rhaamo/ARP-2600/schematics/4022 Noise.pdf

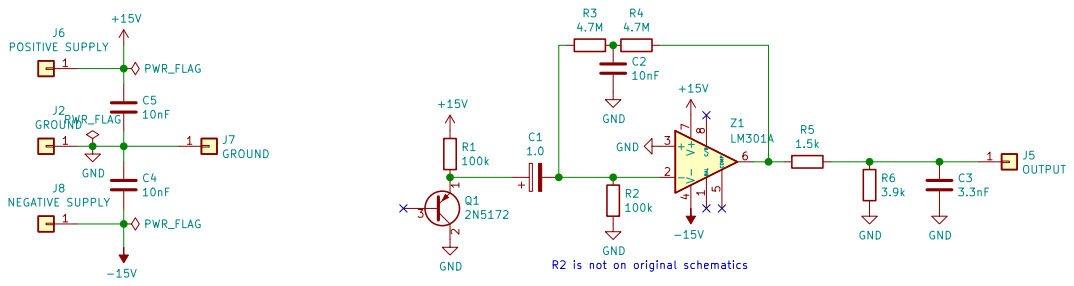
[picture p10: page 1]

R2 is not on original schematics

Id: 1/1 Title: File: 4022 Noise.sch Sheet: /
