rhaamo/ARP-2600/schematics/Board 1.pdf

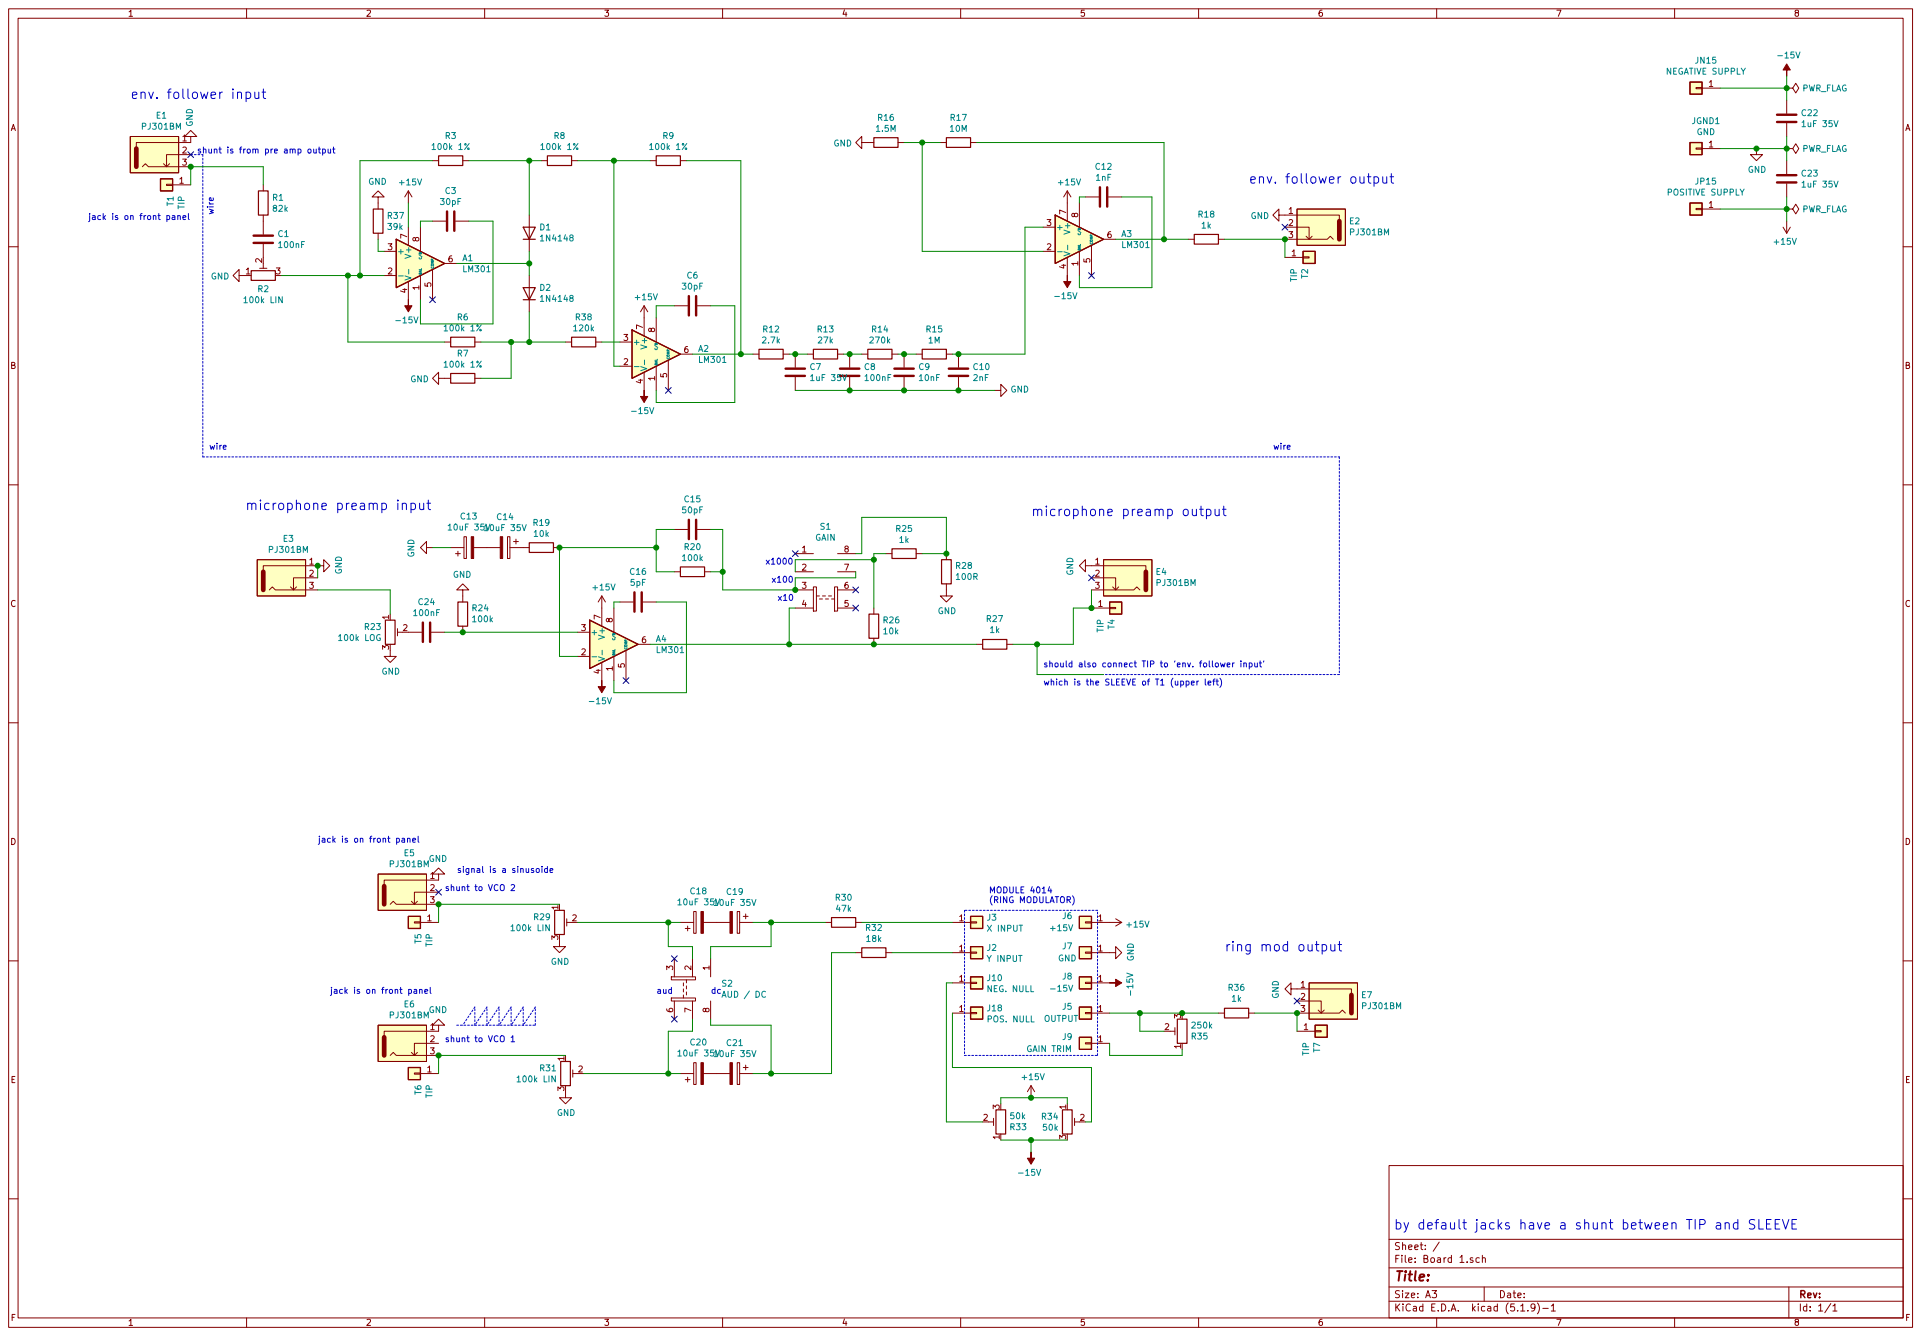
[picture p16: page 1]

shunt is from pre amp output

jack is on front panel

should also connect TIP to 'env. follower input' MODULE 4014

which is the SLEEVE of T1 (upper left) dc

by default jacks have a shunt between TIP and SLEEVE
