rhaamo/ARP-2600/schematics/4020 ADSR.pdf

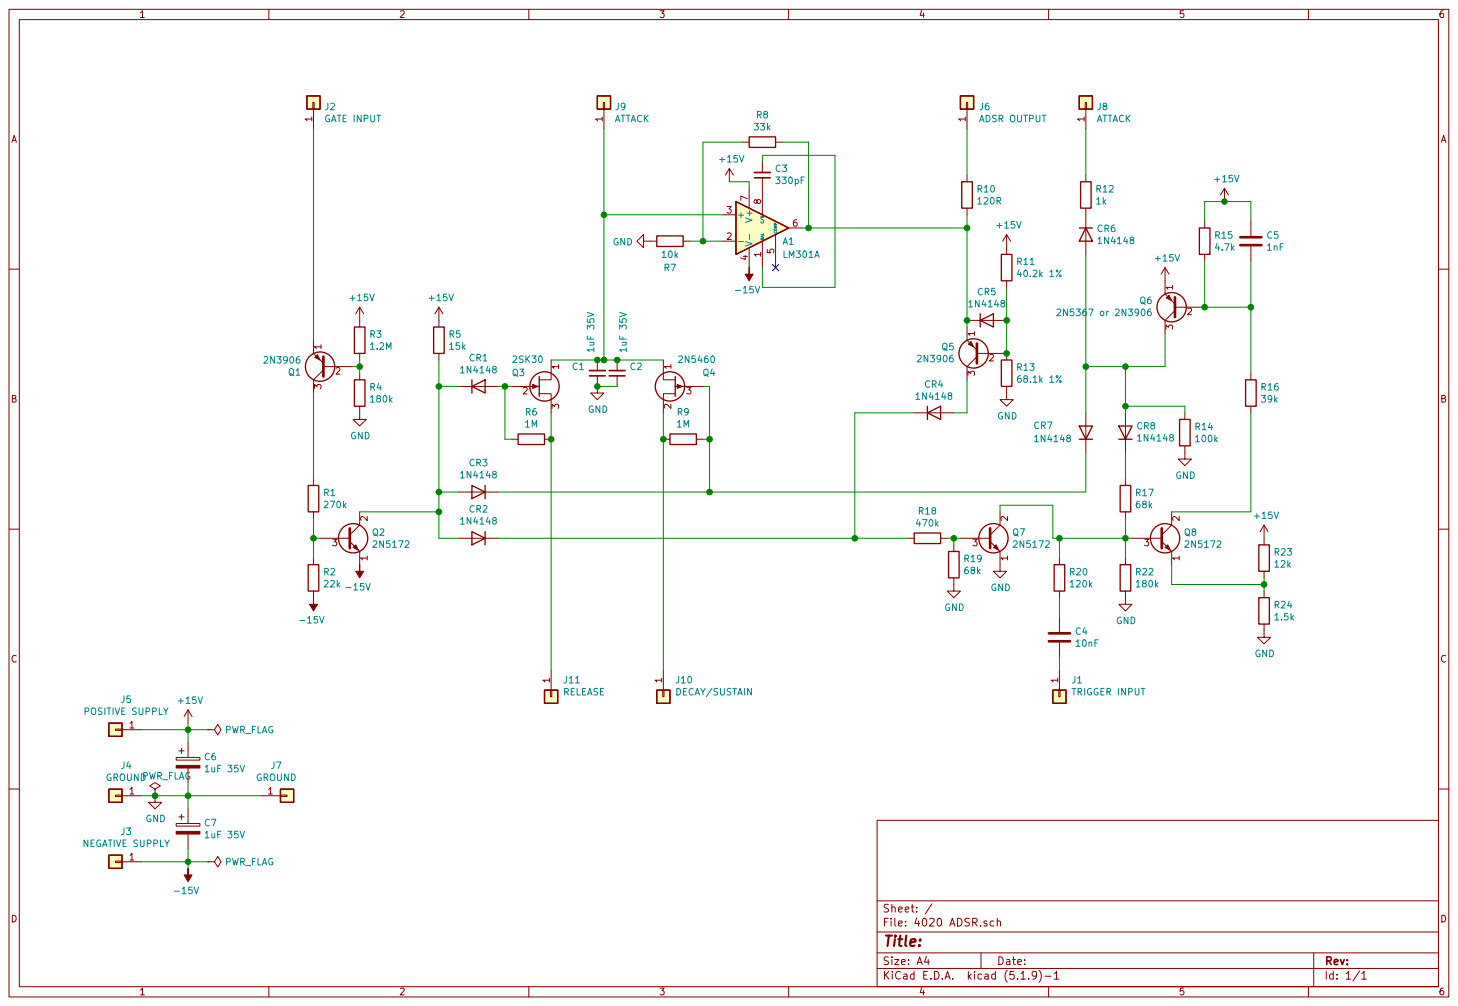
[picture p17: page 1]

Id: 1/1 Title: File: 4020 ADSR.sch Sheet: /
