rhaamo/ARP-2600/Board 1/Board 1.kicad_pcb

## KiCad design kicad/battery_checker.kicad_sch

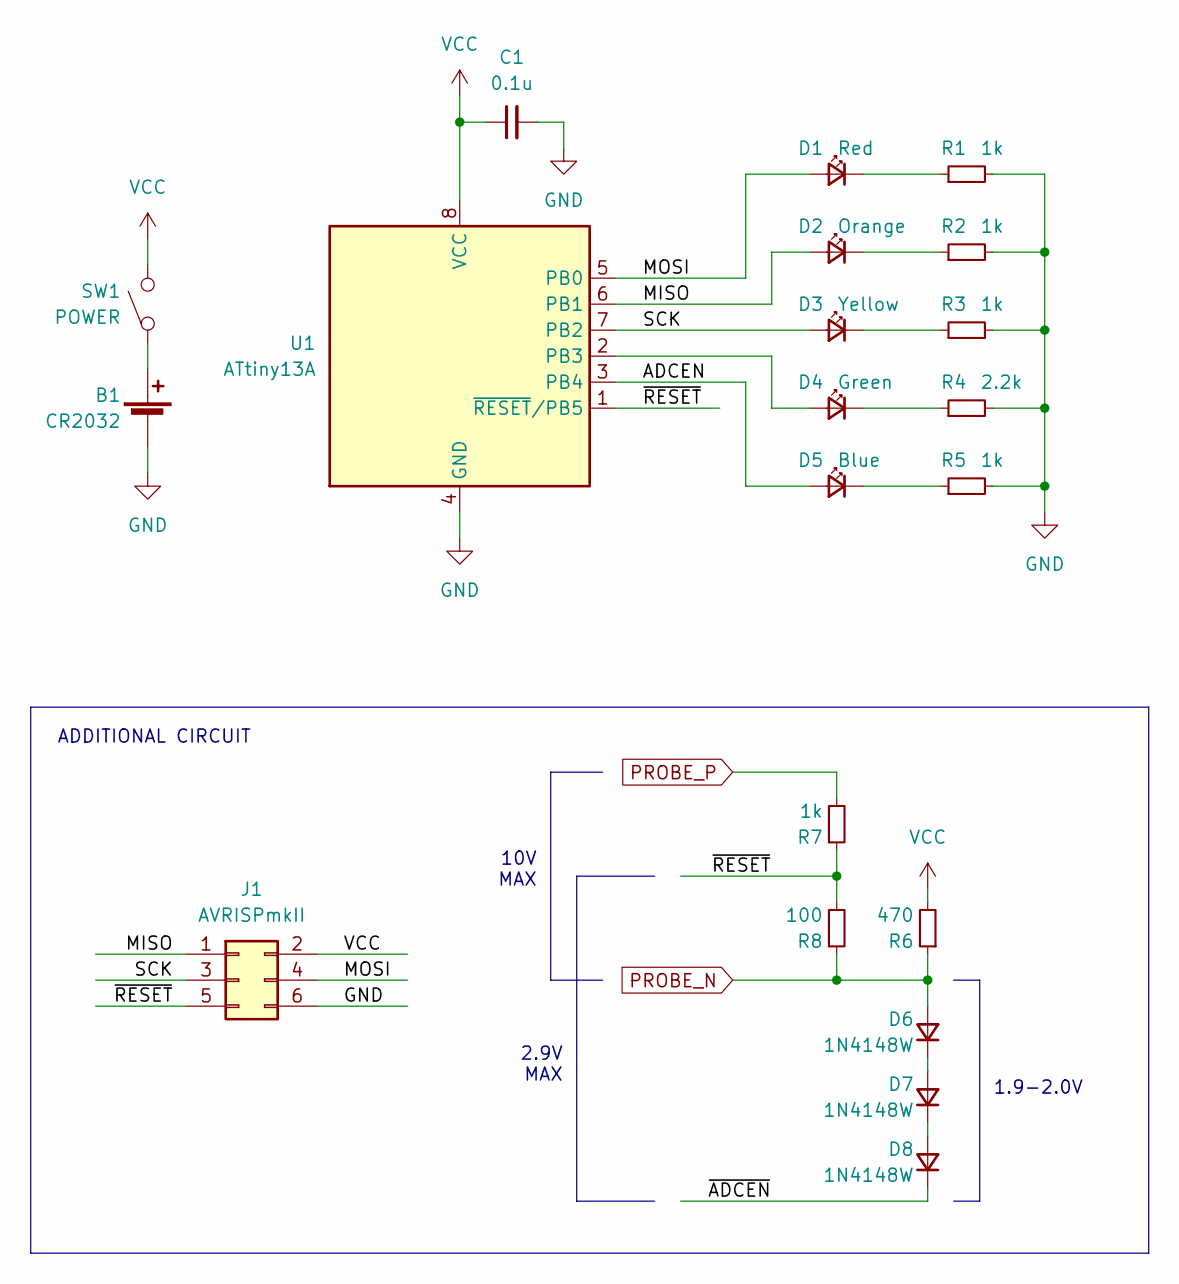
[picture p18: schematic battery_checker.kicad_sch]

Parts:
B1: CR2032
C1: 0.1u
D1: Red
D2: Orange
D3: Yellow
D4: Green
D5: Blue
D6, D7, D8: 1N4148W
J1: AVRISPmkII
R1, R2, R3, R5, R7: 1k
R4: 2.2k
R6: 470
R8: 100
SW1: POWER
U1: ATtiny13A; SOIC-8W_5.3x5.3mm_P1.27mm

Connections:
ADCEN: D5.2 (A), U1.3 (PB4)
GND: J1.6
MISO: D2.2 (A), J1.1, U1.6 (PB1)
MOSI: D1.2 (A), J1.4, U1.5 (PB0)
unnamed: B1.1 (+), SW1.~
unnamed: C1.1, U1.8 (VCC)
unnamed: D1.1 (K), R1.1
unnamed: D2.1 (K), R2.1
unnamed: D3.1 (K), R3.1
unnamed: D4.1 (K), R4.1
unnamed: D4.2 (A), U1.2 (PB3)
unnamed: D5.1 (K), R5.1
unnamed: D6.1 (K), D7.2 (A)
unnamed: D7.1 (K), D8.2 (A)
unnamed: R1.2, R2.2, R3.2, R4.2, R5.2
PROBE_N: D6.2 (A), R6.1, R8.1
PROBE_P: R7.2
SCK: D3.2 (A), J1.3, U1.7 (PB2)
VCC: J1.2
~ADCEN: D8.1 (K)
~RESET: J1.5, R7.1, R8.2, U1.1 (~RESET/PB5)

Notes on the sheet:
ADDITIONAL CIRCUIT
2.9V MAX
10V MAX
1.9-2.0V
